OpenActuator/CoilWinder/Modeling_FreeCAD/SlidePillar.FCStd

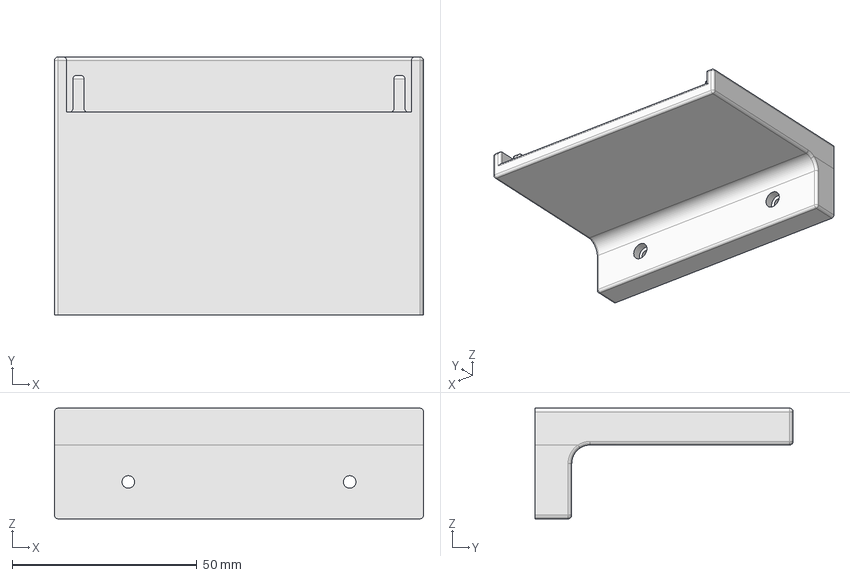
[picture p18: CAD file, 2017-01-22]
Modeling_FreeCAD/SlidePillar.FCStd
100.0 x 70.0 x 30.0 mm
