OpenActuator/CoilWinder/Modeling_FreeCAD/Connector.FCStd

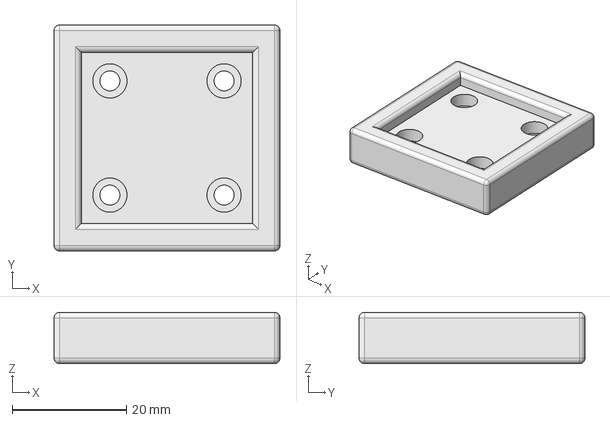
[picture p19: CAD file, 2017-01-22]
Modeling_FreeCAD/Connector.FCStd
39.6 x 39.6 x 9.00 mm
