OpenActuator/CoilWinder/Modeling_FreeCAD/Arduino-Nano.FCStd

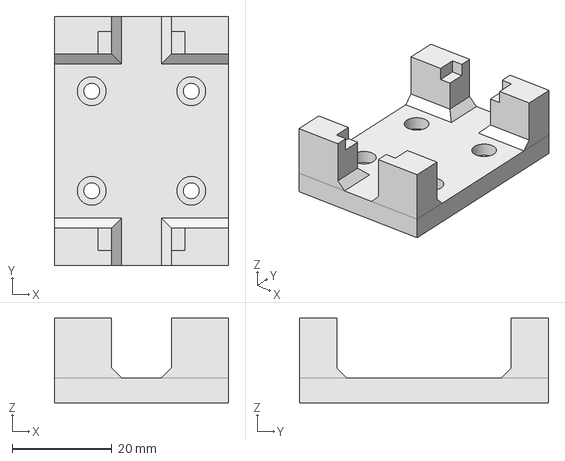
[picture p20: CAD file, 2017-01-22]
Modeling_FreeCAD/Arduino-Nano.FCStd
35.0 x 50.0 x 17.0 mm
