OpenActuator/CoilWinder/Modeling_FreeCAD/SlideSocket.FCStd

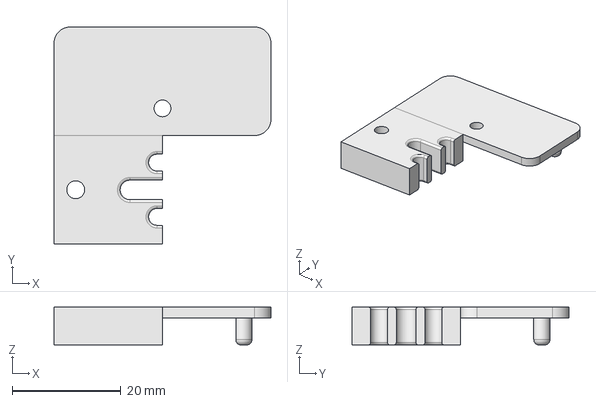
[picture p21: CAD file, 2017-01-22]
Modeling_FreeCAD/SlideSocket.FCStd
40.0 x 40.0 x 7.00 mm
