OpenActuator/CoilWinder/Modeling_FreeCAD/L9110.FCStd

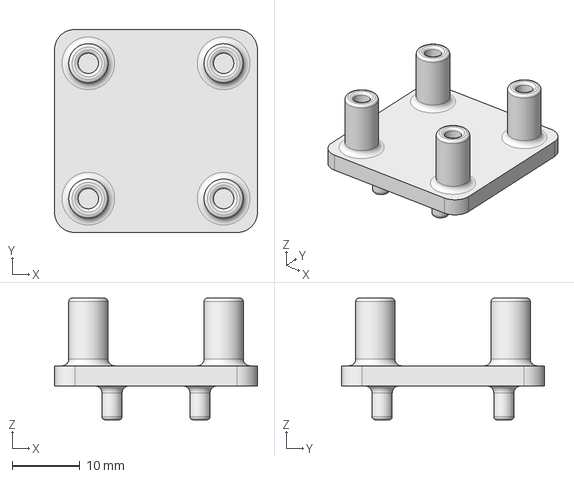
[picture p22: CAD file, 2017-01-22]
Modeling_FreeCAD/L9110.FCStd
30.0 x 30.0 x 18.0 mm
