OpenActuator/CoilWinder/Modeling_FreeCAD/DC-Convertor.FCStd

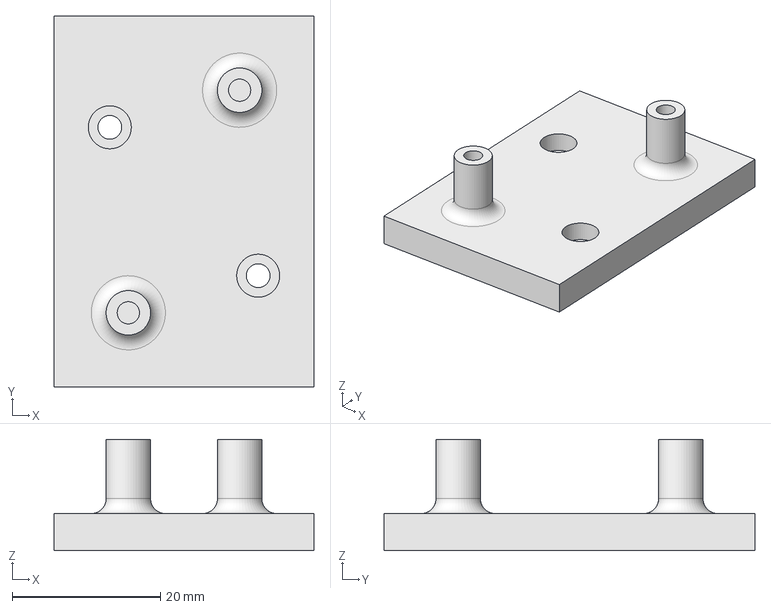
[picture p23: CAD file, 2017-01-22]
Modeling_FreeCAD/DC-Convertor.FCStd
35.0 x 50.0 x 15.0 mm
